bfarago/B3-38A/rv_doc/IMG_20190602_202826.jpg

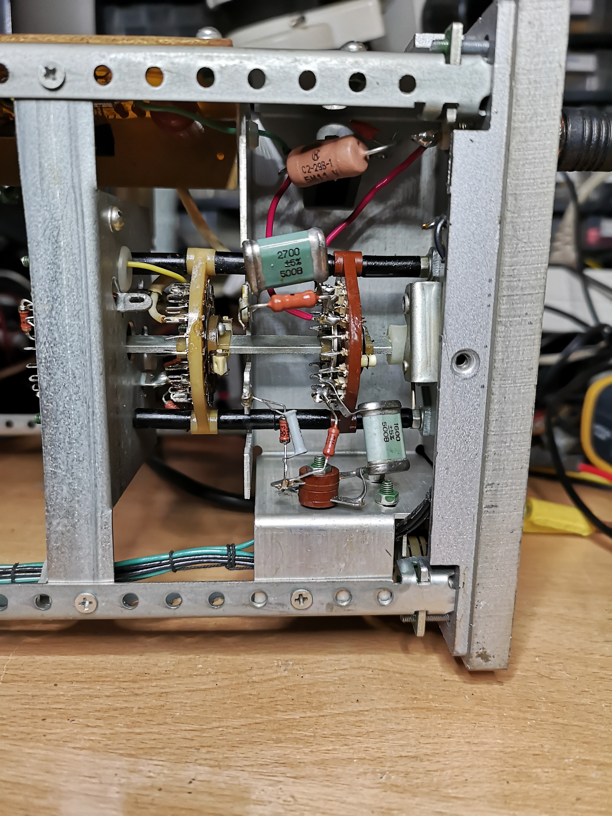
rv_doc/IMG_20190602_202826.jpg
