bfarago/B3-38A/rv_doc/IMG_20190602_202939.jpg

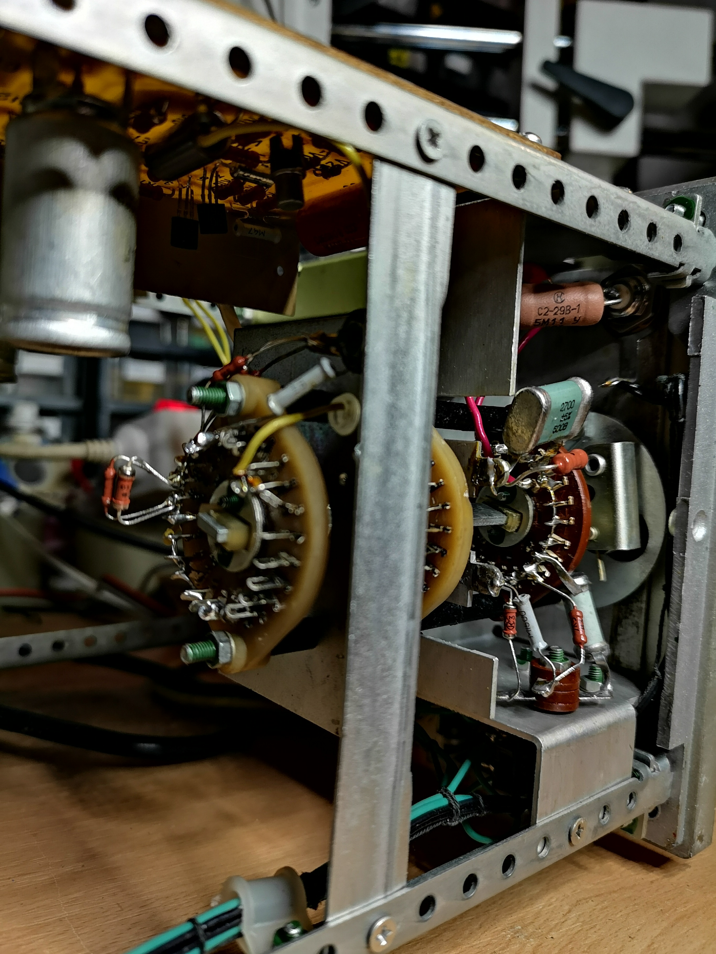
rv_doc/IMG_20190602_202939.jpg
